wherelse/STM32F103-Coreboard/code/SOLGUI/src/MyOLED.c

#include "includeFile.h"
#include "MyOLED.h"


#define OLED_SCL PTE1_OUT		 //D0
#define OLED_SDA PTG0_OUT		 //D1
#define OLED_RST PTG1_OUT	     //RST
#define OLED_DC  PTG2_OUT		 //DS
#define OLED_CS  PTG3_OUT		 //CS

#define XLevelL		0x00
#define XLevelH		0x10
#define XLevel		((XLevelH&0x0F)*16+XLevelL)
#define Max_Column	128
#define Max_Row		64
#define	Brightness	0xCF

/*
4线SPI使用说明：
VBT 供内部DC-DC电压，3.3~4.3V，如果使用5V电压，为保险起见串一个100~500欧的电阻
VCC 供内部逻辑电压 1.8~6V
GND 地

BS0 低电平
BS1 低电平
BS2 低电平

CS  片选管脚
DC  命令数据选择管脚
RES 模块复位管脚
D0（SCLK） ，时钟脚，由MCU控制
D1（MOSI） ，主输出从输入数据脚，由MCU控制

D2 悬空
D3-D7 ， 低电平 ， 也可悬空，但最好设为低电平
RD  低电平 ，也可悬空，但最好设为低电平
RW  低电平 ，也可悬空，但最好设为低电平
RD  低电平 ，也可悬空，但最好设为低电平
*/

#define X_WIDTH 128
#define Y_WIDTH 64
//======================================
const u8 F6x8[][6] =
{
    { 0x00, 0x00, 0x00, 0x00, 0x00, 0x00 },   // sp
    { 0x00, 0x00, 0x00, 0x2f, 0x00, 0x00 },   // !
    { 0x00, 0x00, 0x07, 0x00, 0x07, 0x00 },   // "
    { 0x00, 0x14, 0x7f, 0x14, 0x7f, 0x14 },   // #
    { 0x00, 0x24, 0x2a, 0x7f, 0x2a, 0x12 },   // $
    { 0x00, 0x62, 0x64, 0x08, 0x13, 0x23 },   // %
    { 0x00, 0x36, 0x49, 0x55, 0x22, 0x50 },   // &
    { 0x00, 0x00, 0x05, 0x03, 0x00, 0x00 },   // '
    { 0x00, 0x00, 0x1c, 0x22, 0x41, 0x00 },   // (
    { 0x00, 0x00, 0x41, 0x22, 0x1c, 0x00 },   // )
    { 0x00, 0x14, 0x08, 0x3E, 0x08, 0x14 },   // *
    { 0x00, 0x08, 0x08, 0x3E, 0x08, 0x08 },   // +
    { 0x00, 0x00, 0x00, 0xA0, 0x60, 0x00 },   // ,
    { 0x00, 0x08, 0x08, 0x08, 0x08, 0x08 },   // -
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
};


void Dly_ms(u16 ms)
{
   u16 ii,jj;
   if (ms<1) ms=1;
   ms = ms*12 ;
   for(ii=0;ii<ms;ii++)
   //  for(jj=0;jj<1335;jj++);  //16MHz--1ms
  //   for(jj=0;jj<4006;jj++);  //48MHz--1ms
     for(jj=0;jj<5341;jj++);    //64MHz--1ms
}

void OLED_WrDat(u8 data)
{
	u8 i=8;
	//LCD_CS=0;;
	OLED_DC=1;
  OLED_SCL=0;
  //asm("nop");
  while(i--)
  {
    if(data&0x80){OLED_SDA=1;}
    else{OLED_SDA=0;}
    OLED_SCL=1;
    asm("nop");;
		//asm("nop");
    OLED_SCL=0;;
    data<<=1;
  }
	//LCD_CS=1;
}
void OLED_WrCmd(u8 cmd)
{
	u8 i=8;

	//LCD_CS=0;;
	OLED_DC=0;;
  OLED_SCL=0;;
  //asm("nop");
  while(i--)
  {
    if(cmd&0x80){OLED_SDA=1;}
    else{OLED_SDA=0;;}
    OLED_SCL=1;;
    asm("nop");;
		//asm("nop");
    OLED_SCL=0;;
    cmd<<=1;;
  }

}
void OLED_Set_Pos(u8 x, u8 y)
{
  OLED_WrCmd(0xb0+y);
  OLED_WrCmd(((x&0xf0)>>4)|0x10);
  OLED_WrCmd((x&0x0f)|0x01);
}
void OLED_Fill(u8 bmp_data)
{
	u8 y,x;

	for(y=0;y<8;y++)
	{
		OLED_WrCmd(0xb0+y);
		OLED_WrCmd(0x01);
		OLED_WrCmd(0x10);
		for(x=0;x<X_WIDTH;x++)
			OLED_WrDat(bmp_data);
	}
}
void OLED_CLS(void)
{
	u8 y,x;
	for(y=0;y<8;y++)
	{
		OLED_WrCmd(0xb0+y);
		OLED_WrCmd(0x01);
		OLED_WrCmd(0x10);
		for(x=0;x<X_WIDTH;x++)
			OLED_WrDat(0);
	}
}
void OLED_DLY_ms(u16 ms)
{
  u16 a;
  while(ms)
  {
    a=16000;
    while(a--);
    ms--;
  }
  return;
}
/*!
*  @brief      OLED初始化
*  @note       移植注意修改GPIO初始化
*/
void OLED_Init(void)
{

      gpio_init (PTE1, GPO,HIGH);    //
      gpio_init (PTG0, GPO,HIGH);    //
      gpio_init (PTG1, GPO,HIGH);    //
      gpio_init (PTG2, GPO,HIGH);    //
      gpio_init (PTG3, GPO,HIGH);    //初始化引脚

	  OLED_SCL=1;
	  OLED_CS = 0 ; //使能信号端，拉低时正常使用
	  OLED_RST=0;
	  OLED_DLY_ms(50);
	  OLED_RST=1;
	  OLED_WrCmd(0xae);//--turn off oled panel
	  OLED_WrCmd(0x00);//---set low column address
	  OLED_WrCmd(0x10);//---set high column address
	  OLED_WrCmd(0x40);//--set start line address  Set Mapping RAM Display Start Line (0x00~0x3F)
	  OLED_WrCmd(0x81);//--set contrast control register
	  OLED_WrCmd(0xcf); // Set SEG Output Current Brightness
	  OLED_WrCmd(0xa1);//--Set SEG/Column Mapping     0xa0左右反置 0xa1正常
	  OLED_WrCmd(0xc8);//Set COM/Row Scan Direction   0xc0上下反置 0xc8正常
	  OLED_WrCmd(0xa6);//--set normal display
	  OLED_WrCmd(0xa8);//--set multiplex ratio(1 to 64)
	  OLED_WrCmd(0x3f);//--1/64 duty
	  OLED_WrCmd(0xd3);//-set display offset	Shift Mapping RAM Counter (0x00~0x3F)
	  OLED_WrCmd(0x00);//-not offset
	  OLED_WrCmd(0xd5);//--set display clock divide ratio/oscillator frequency
	  OLED_WrCmd(0x80);//--set divide ratio, Set Clock as 100 Frames/Sec
	  OLED_WrCmd(0xd9);//--set pre-charge period
	  OLED_WrCmd(0xf1);//Set Pre-Charge as 15 Clocks & Discharge as 1 Clock
	  OLED_WrCmd(0xda);//--set com pins hardware configuration
	  OLED_WrCmd(0x12);
	  OLED_WrCmd(0xdb);//--set vcomh
	  OLED_WrCmd(0x40);//Set VCOM Deselect Level
	  OLED_WrCmd(0x20);//-Set Page Addressing Mode (0x00/0x01/0x02)
	  OLED_WrCmd(0x02);//
	  OLED_WrCmd(0x8d);//--set Charge Pump enable/disable
	  OLED_WrCmd(0x14);//--set(0x10) disable
	  OLED_WrCmd(0xa4);// Disable Entire Display On (0xa4/0xa5)
	  OLED_WrCmd(0xa6);// Disable Inverse Display On (0xa6/a7)
	  OLED_WrCmd(0xaf);//--turn on oled panel
	  OLED_Fill(0x00);  //初始清屏
	  OLED_Set_Pos(0,0);

}
//==============================================================
//函数名： void LCD_PutPixel(u8 x,u8 y)
//功能描述：绘制一个点（x,y）
//参数：真实坐标值(x,y),x的范围0～127，y的范围0～64
//返回：无
//==============================================================
void OLED_PutPixel(u8 x,u8 y)
{
	u8 data1;  //data1当前点的数据

  OLED_Set_Pos(x,y);
	data1 = 0x01<<(y%8);
	OLED_WrCmd(0xb0+(y>>3));
	OLED_WrCmd(((x&0xf0)>>4)|0x10);
	OLED_WrCmd((x&0x0f)|0x00);
	OLED_WrDat(data1);
}
//==============================================================
//函数名： void LCD_Rectangle(u8 x1,u8 y1,
//                   u8 x2,u8 y2,u8 color,u8 gif)
//功能描述：绘制一个实心矩形
//参数：左上角坐标（x1,y1）,右下角坐标（x2，y2）
//      其中x1、x2的范围0～127，y1，y2的范围0～63，即真实坐标值
//返回：无
//==============================================================
void OLED_Rectangle(u8 x1,u8 y1,u8 x2,u8 y2,u8 gif)
{
	u8 n;

	OLED_Set_Pos(x1,y1>>3);
	for(n=x1;n<=x2;n++)
	{
		OLED_WrDat(0x01<<(y1%8));
		if(gif == 1) 	OLED_DLY_ms(50);
	}
	OLED_Set_Pos(x1,y2>>3);
  for(n=x1;n<=x2;n++)
	{
		OLED_WrDat(0x01<<(y2%8));
		if(gif == 1) 	OLED_DLY_ms(5);
	}

}
//==============================================================
//函数名：LCD_P6x8Str(u8 x,u8 y,u8 *p)
//功能描述：写入一组标准ASCII字符串
//参数：显示的位置（x,y），y为页范围0～7，要显示的字符串
//返回：无
//==============================================================
void OLED_P6x8Str(u8 x,u8 y,u8 ch[])
{
  u8 c=0,i=0,j=0;
  while (ch[j]!='\0')
  {
    c =ch[j]-32;
    if(x>126){x=0;y++;}
    OLED_Set_Pos(x,y);
  	for(i=0;i<6;i++)
  	  OLED_WrDat(F6x8[c][i]);
  	x+=6;
  	j++;
  }
}
//==============================================================
//函数名：LCD_P8x16Str(u8 x,u8 y,,u8 t,u8 *p)
//功能描述：写入一组标准ASCII字符串
//参数：显示的位置（x,y），y为页范围0～7，要显示的字符串
//t 0正常显示  1反显
//返回：无
//==============================================================
void OLED_P8x16Str(u8 x,u8 y,u8 t,u8 ch[])
{
  u8 c=0,i=0,j=0;

  while (ch[j]!='\0')
  {
    c =ch[j]-32;
    if(x>120){x=0;y++;}
    OLED_Set_Pos(x,y);
  	for(i=0;i<8;i++)
        {
          if(t==0)
  	  OLED_WrDat(F8X16[c*16+i]);
          else OLED_WrDat(~F8X16[c*16+i]);
        }
  	OLED_Set_Pos(x,y+1);
  	for(i=0;i<8;i++)
        {
          if(t==0)
  	  OLED_WrDat(F8X16[c*16+i+8]);
          else OLED_WrDat(~F8X16[c*16+i+8]);
        }
  	x+=8;
  	j++;
  }
}


//==============================================================
//函数名： void Draw_BMP(u8 x,u8 y)
//功能描述：显示BMP图片128×64
//参数：起始点坐标(x,y),x的范围0～127，y为页的范围0～7
//返回：无
//==============================================================
void Draw_BMP(u8 x0,u8 y0,u8 x1,u8 y1,u8 bmp[])
{
  u16 ii=0;
  u8 x,y;

  if(y1%8==0) y1=y1/8;
  else y1=y1/8+1;
	for(y=0;y<=6;y++)
	{
		OLED_Set_Pos(0,y);
    for(x=0;x<128;x++)
	    {
	    	OLED_WrDat(bmp[ii++]);
	    }
	}
}
//画飞机
void Draw_LibLogo(void)
{
  u16 ii=0;
  u8 x,y;

	for(y=0;y<8;y++)
	{
		OLED_Set_Pos(34,y);
    for(x=34;x<94;x++)
	    {
	    	OLED_WrDat(LIBLOGO60x58[ii++]);
	    }
	}
}






void Display_Value(u8 x,u8 y,u8 t,float Value)
{
  u8 Arry[10];
  ToSting(Value,Arry);
  OLED_P8x16Str(x,y,t,Arry);
}


/*!
*  @brief      OLED填充函数 移植GUI用
*  @author	   Jassy
*  @date       20161130
*  @param	   bmp[128][8] 二维数组填充 
*/
void pixelC_HW_OLED_FillScreen(u8 bmp[128][8])
{
	u8 x, y;
	for (y = 0; y < 8; y++)
	{
		OLED_Set_Pos(0, y);
		for (x = 0; x < 128; x++)
		{
			OLED_WrDat(bmp[x][y]);
		}
	}
}
/*!
*  @brief      画车队标志
*  @author	   Jassy
*  @date       20170319
*/
void draw_cauc_logo(void)
{
	Draw_BMP(0, 0, 128, 64, cauc_logo);
	OLED_P6x8Str(52, 6, "CAUC");
	OLED_P6x8Str(4, 7, "Intelligent Car Team");
}
