wherelse/STM32F103-Coreboard/code/HARDWARE/LED/led.c

#include "led.h"

//////////////////////////////////////////////////////////////////////////////////	 
//本程序只供学习使用，未经作者许可，不得用于其它任何用途
//ALIENTEK战舰STM32开发板
//LED驱动代码	   
//正点原子@ALIENTEK
//技术论坛:www.openedv.com
//修改日期:2012/9/2
//版本：V1.0
//版权所有，盗版必究。
//Copyright(C) 广州市星翼电子科技有限公司 2009-2019
//All rights reserved									  
////////////////////////////////////////////////////////////////////////////////// 	   

//初始化PB5和PE5为输出口.并使能这两个口的时钟		    
//LED IO初始化
void LED_Init(void)
{
 
 GPIO_InitTypeDef  GPIO_InitStructure;
 	
 RCC_APB2PeriphClockCmd(RCC_APB2Periph_GPIOB|RCC_APB2Periph_AFIO, ENABLE);	 //使能PC端口时钟
GPIO_PinRemapConfig(GPIO_Remap_SWJ_JTAGDisable, ENABLE); 
	
 GPIO_InitStructure.GPIO_Pin = GPIO_Pin_3;				 //LED1-->PC.15 端口配置
 GPIO_InitStructure.GPIO_Mode = GPIO_Mode_Out_PP; 		 //推挽输出
 GPIO_InitStructure.GPIO_Speed = GPIO_Speed_2MHz;		 //IO口速度为50MHz
 GPIO_Init(GPIOB, &GPIO_InitStructure);					 //根据设定参数初始化GPIOC.15
 GPIO_ResetBits(GPIOB,GPIO_Pin_3);						 //PC.15 输出高

}
 
