wherelse/STM32F103-Coreboard/code/HARDWARE/BEEP/beep.c

#include "beep.h"
#include "includeFile.h"
	    
//蜂鸣器初始化
void BEEP_Init(void)
{
 
 GPIO_InitTypeDef  GPIO_InitStructure;
 	
 RCC_APB2PeriphClockCmd(RCC_APB2Periph_GPIOC, ENABLE);	 //使能GPIOB端口时钟
 
 GPIO_InitStructure.GPIO_Pin = GPIO_Pin_13;				 //BEEP-->PB.8 端口配置
 GPIO_InitStructure.GPIO_Mode = GPIO_Mode_Out_PP; 		 //推挽输出
 GPIO_InitStructure.GPIO_Speed = GPIO_Speed_10MHz;	 //速度为50MHz
 GPIO_Init(GPIOC, &GPIO_InitStructure);	 //根据参数初始化GPIOB.8
 
 GPIO_ResetBits(GPIOC,GPIO_Pin_13);//输出0，关闭蜂鸣器输出

}


void Beeptimes(unsigned char times)
{
	unsigned char i;
    for (i = 0; i < times; i++)
    {
        BEEP = 1;
        delay_ms(50);
        BEEP = 0;
        delay_ms(50);
    }
}
