wherelse/STM32F103-Coreboard/code/USER/includeFile.h

#ifndef __INCLUDEFILE_H
#define __INCLUDEFILE_H 

#include "sys.h"
#include "delay.h"
#include "usart.h"
#include "key.h"
#include "led.h"
#include "timer.h"
#include "beep.h"
#include "oled.h"
#include "stmflash.h"
#include "wdg.h"
#include "exti.h"
#include "pwm.h"
#include "control.h"
#include "main.h"
#include "adc.h"
#include "math.h"
#include "usb_lib.h"
#include "hw_config.h"
#include "usb_pwr.h"
#include "SOLGUI_Include.h"
#include "max44009.h"
#endif
